rianadon/touchapad/arduino/corners.h

#define GREY 0x39c7
#define LTGREY 0xbdd7
#define DKGREY 0x4208
#define GREEN 0x0788
uint16_t CORNER_WHITE[4][4] = {
    {0x0000, 0x3166, 0xbdd7, 0xf7be},
    {0x2965, 0xef5d, 0xffff, 0xffff},
    {0xc618, 0xffff, 0xffff, 0xffff},
    {0xffdf, 0xffff, 0xffff, 0xffff},
};
uint16_t CORNER_GREY[4][4] = {
    {0x0000, 0x0841, 0x2945, 0x39c7},
    {0x0841, 0x31a6, 0x39e7, 0x39c7},
    {0x2945, 0x39e7, 0x39c7, 0x39c7},
    {0x39c7, 0x39c7, 0x39c7, 0x39c7},
};
uint16_t CORNER_LTGREY[4][4] = {
    {0x0000, 0x2104, 0x8c71, 0xb5b6},
    {0x2104, 0xad55, 0xc638, 0xbdd7},
    {0x8c71, 0xc638, 0xb5b6, 0xbdd7},
    {0xbdb7, 0xbdd7, 0xbdd7, 0xbdd7},
};
uint16_t CORNER_BLACK_HG[4][4] = {
    {0xc618, 0xa4f4, 0x31a6, 0x0841},
    {0xa4f4, 0x1082, 0x0000, 0x0000},
    {0x3166, 0x0000, 0x0020, 0x0000},
    {0x0020, 0x0000, 0x0000, 0x0000},
};
uint16_t CORNER_BLACK_LG[2][2] = {
    {0x8c51, 0x4a49},
    {0x4a49, 0x41e8},
};
uint16_t CORNER_BLACK_SM[1][1] = {
    {0x5acb},
};
uint16_t CORNER_GREEN_LG[2][2] = {
    {0xa7d7, 0x1f89},
    {0x1789, 0x0787},
};
uint16_t CORNER_GREEN_SM[1][1] = {
    {0x37ad},
};
